sasiela/pitalk-pro/photos/IMG_3596.jpeg

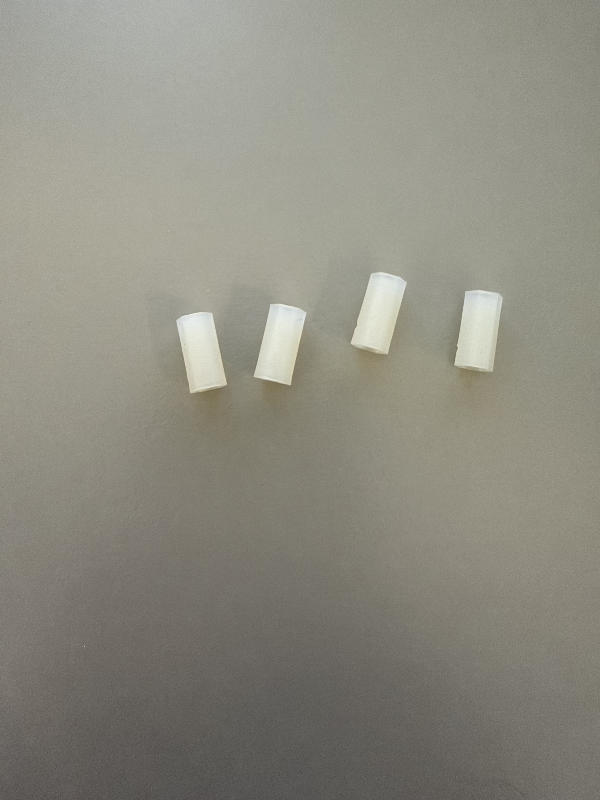
photos/IMG_3596.jpeg
