sasiela/pitalk-pro/photos/IMG_3599.jpeg

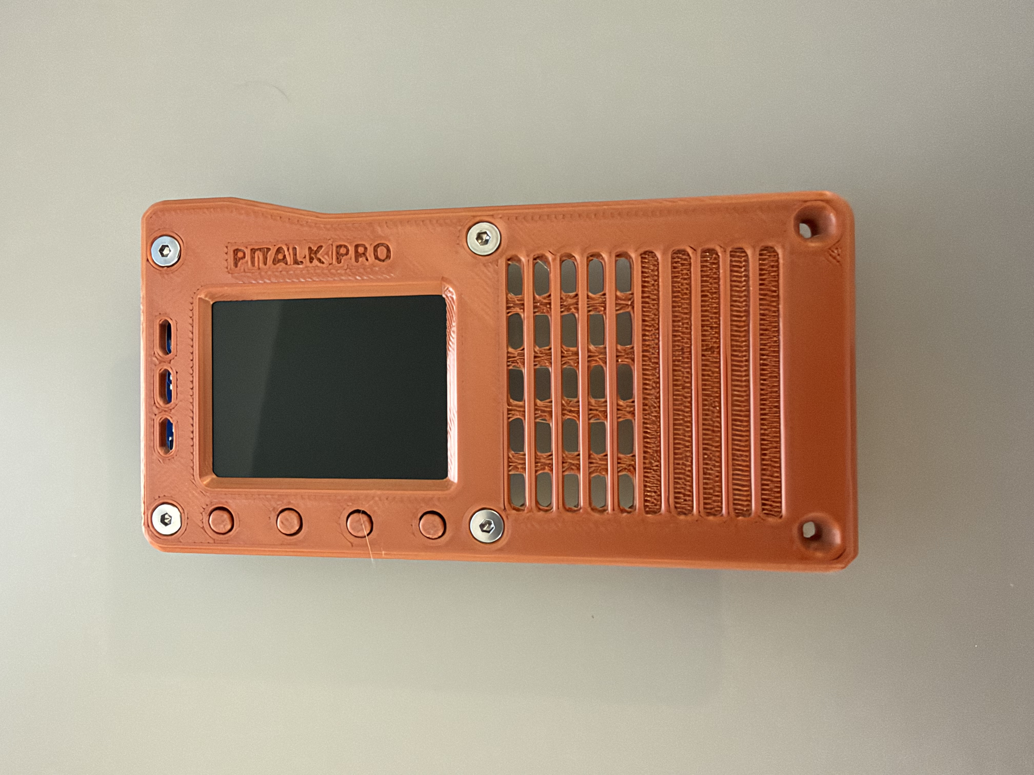
photos/IMG_3599.jpeg
