sasiela/pitalk-pro/photos/IMG_3600.jpeg

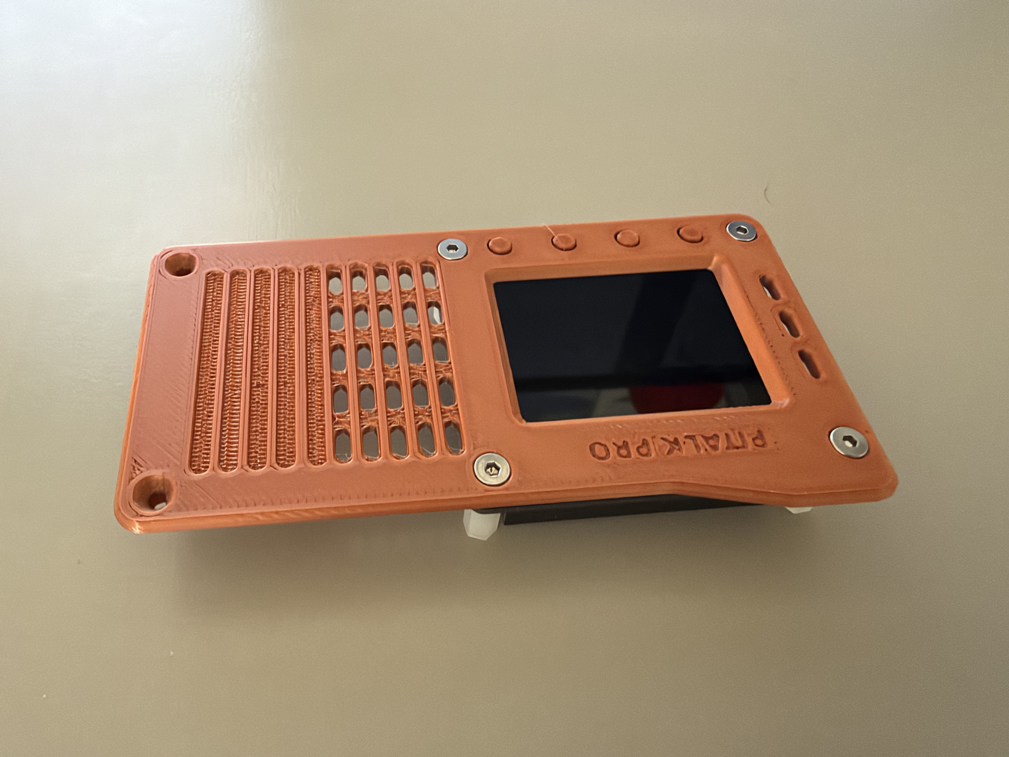
photos/IMG_3600.jpeg
