sasiela/pitalk-pro/photos/IMG_3602.jpeg

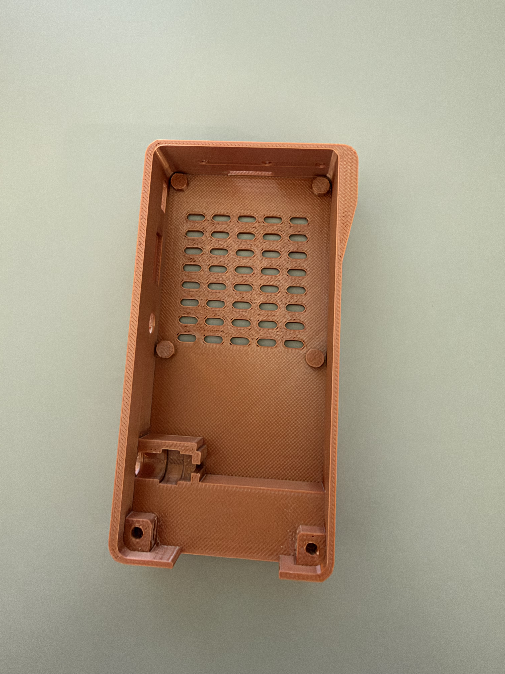
photos/IMG_3602.jpeg
