sasiela/pitalk-pro/photos/IMG_3603.jpeg

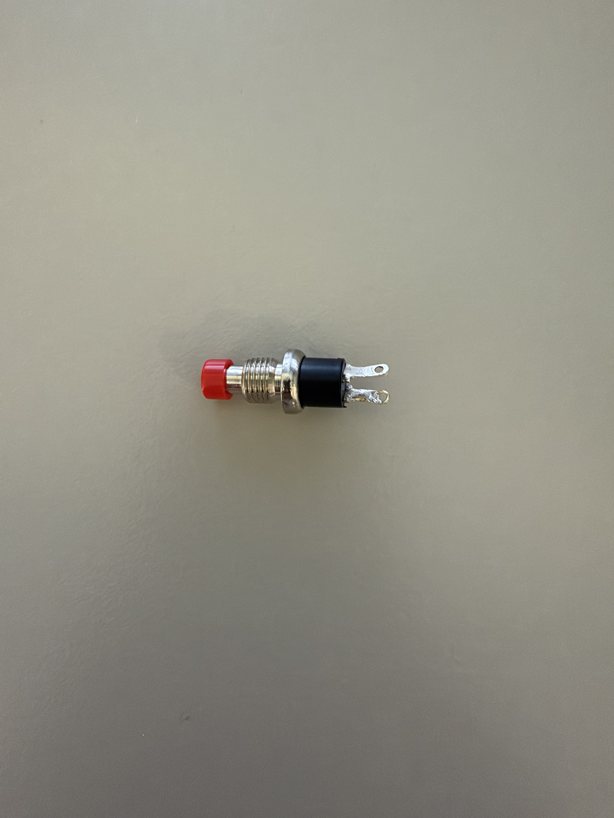
photos/IMG_3603.jpeg
