sasiela/pitalk-pro/photos/IMG_3605.jpeg

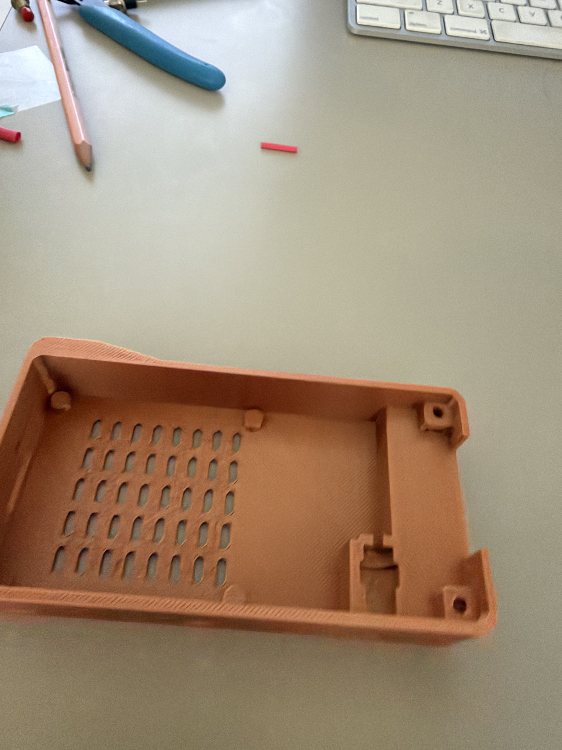
photos/IMG_3605.jpeg
