sasiela/pitalk-pro/photos/IMG_3606.jpeg

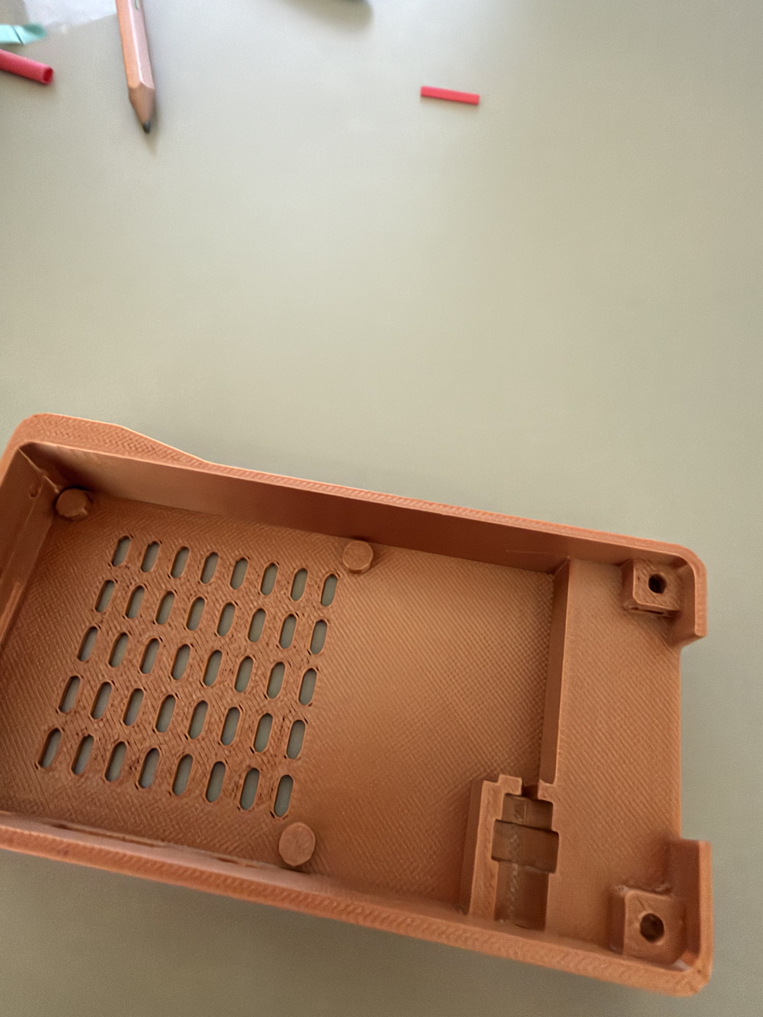
photos/IMG_3606.jpeg
