sasiela/pitalk-pro/photos/IMG_3607.jpeg

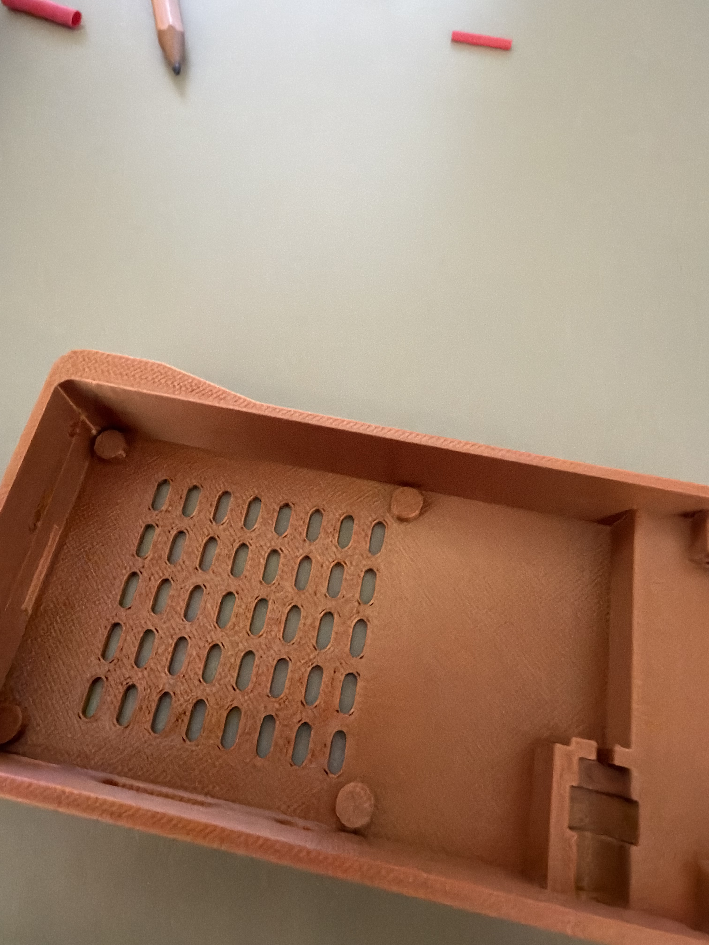
photos/IMG_3607.jpeg
