sasiela/pitalk-pro/photos/IMG_3610.jpeg

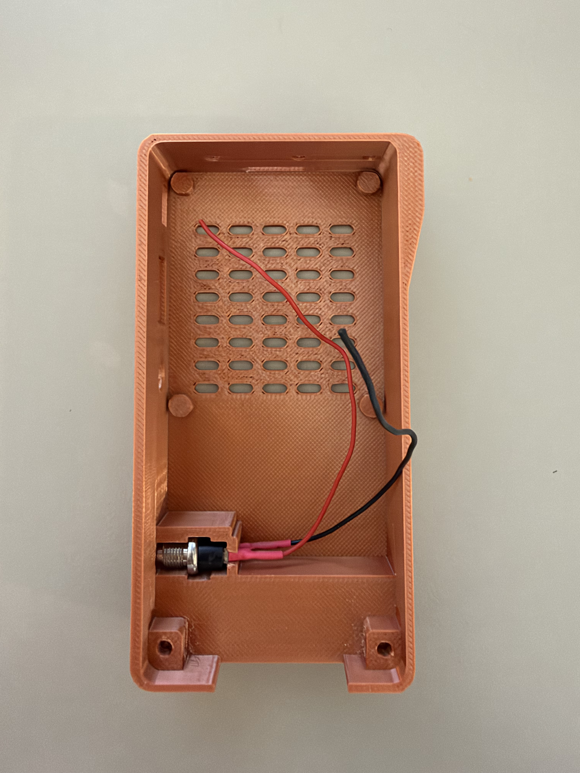
photos/IMG_3610.jpeg
