sasiela/pitalk-pro/photos/IMG_3612.jpeg

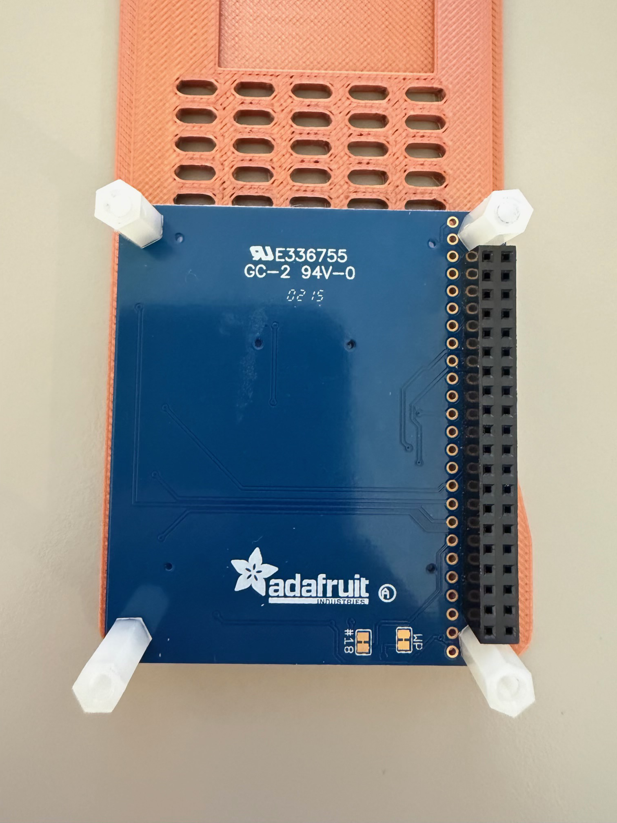
photos/IMG_3612.jpeg
