sasiela/pitalk-pro/photos/IMG_3614.jpeg

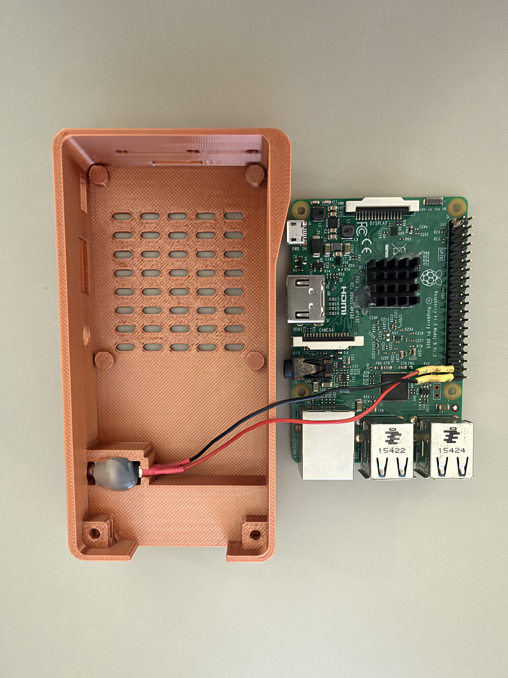
photos/IMG_3614.jpeg
