sasiela/pitalk-pro/photos/IMG_3616.jpeg

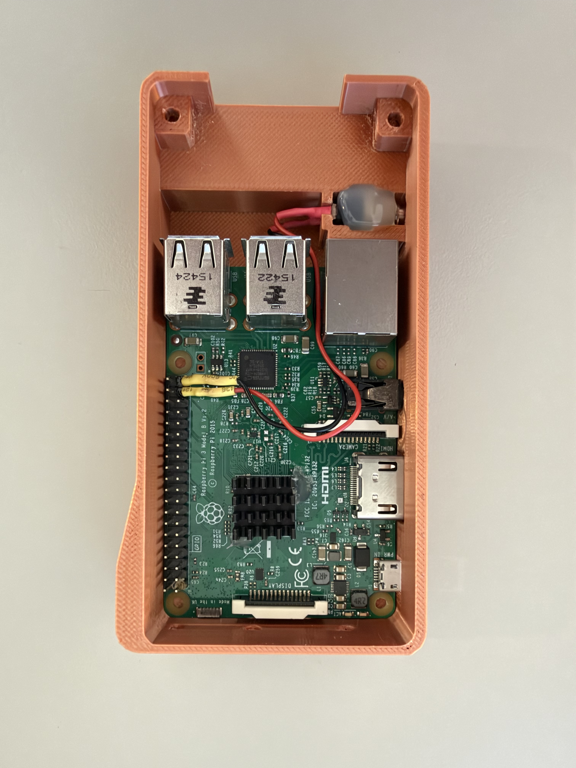
photos/IMG_3616.jpeg
